discover1977/Wi-Fi-WEB-radio/Photo/20170609_091035.jpg

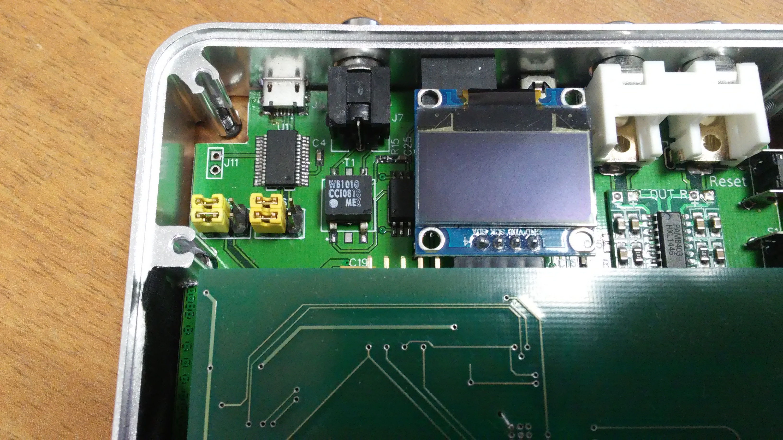
Photo/20170609_091035.jpg
