discover1977/Wi-Fi-WEB-radio/Photo/IMG_8502.JPG

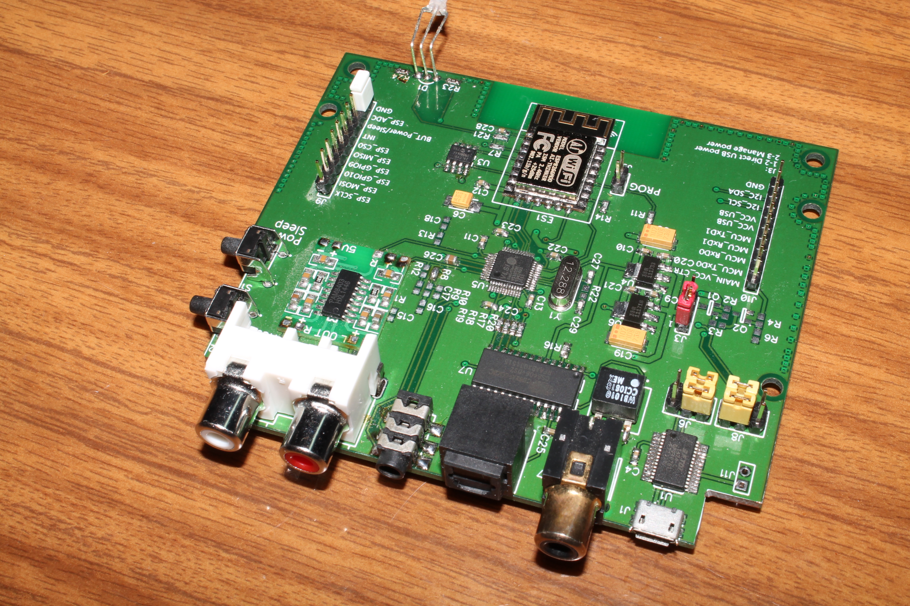
Photo/IMG_8502.JPG
