discover1977/Wi-Fi-WEB-radio/Photo/IMG_8504.JPG

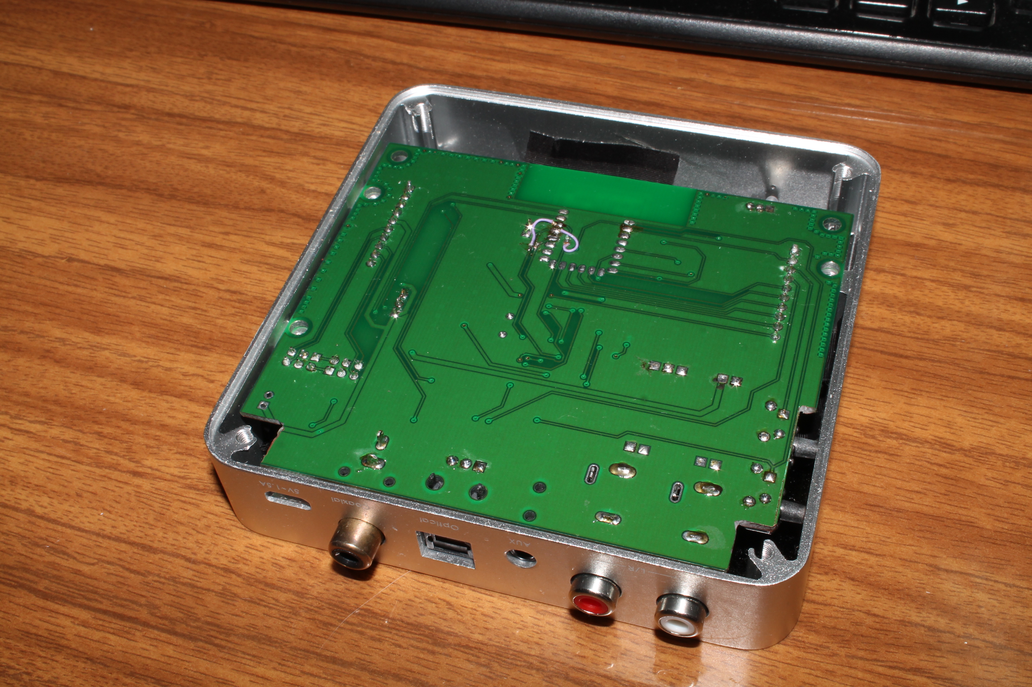
Photo/IMG_8504.JPG
