discover1977/Wi-Fi-WEB-radio/Photo/IMG_8505.JPG

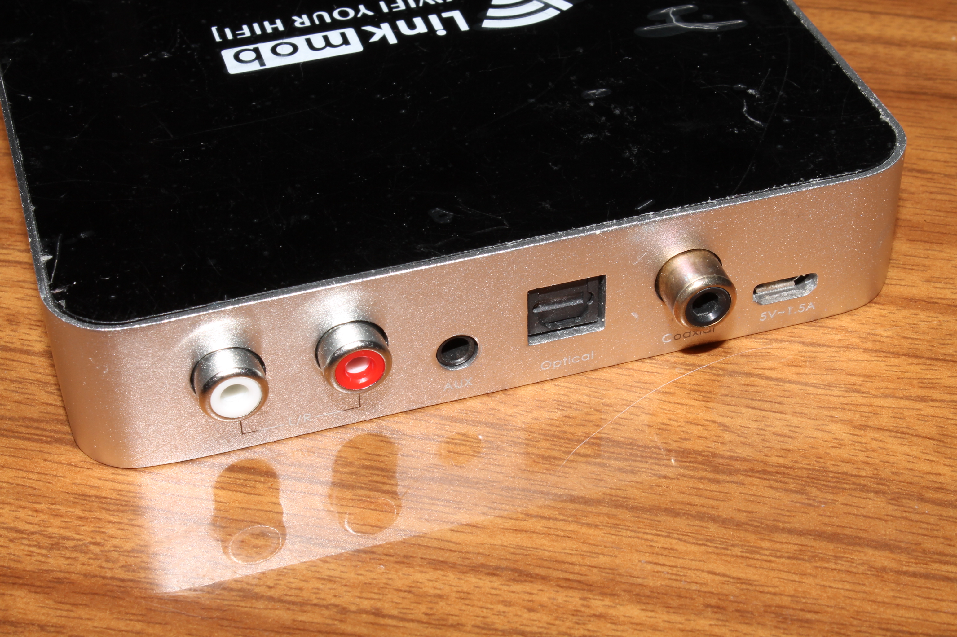
Photo/IMG_8505.JPG
