discover1977/Wi-Fi-WEB-radio/Photo/IMG_8543.JPG

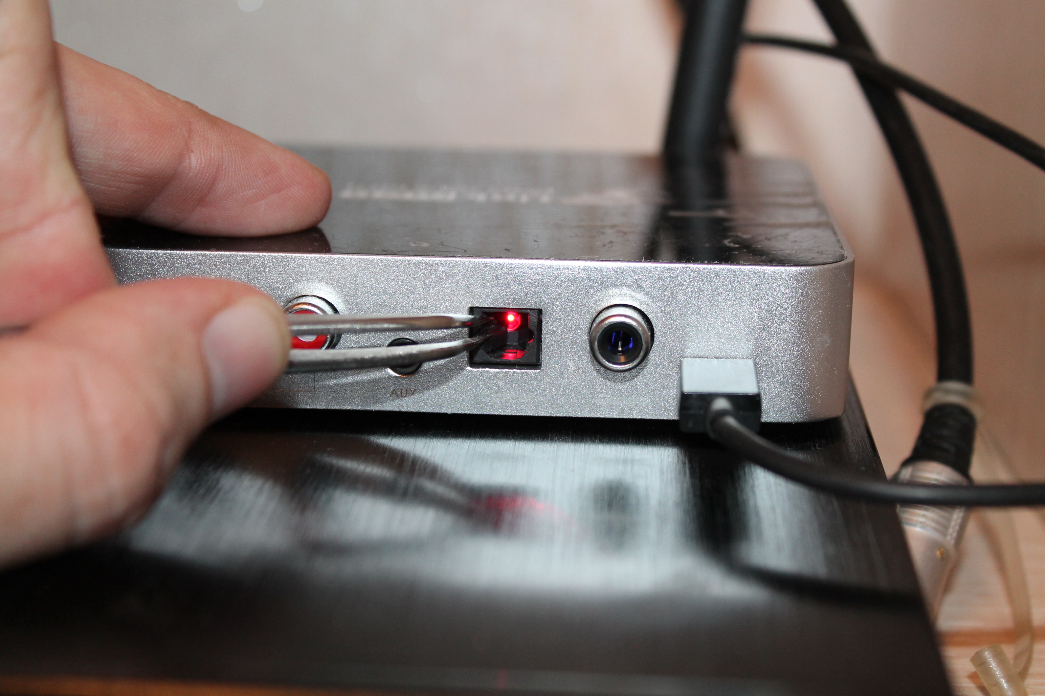
Photo/IMG_8543.JPG
