discover1977/Wi-Fi-WEB-radio/Photo/IMG_8549.JPG

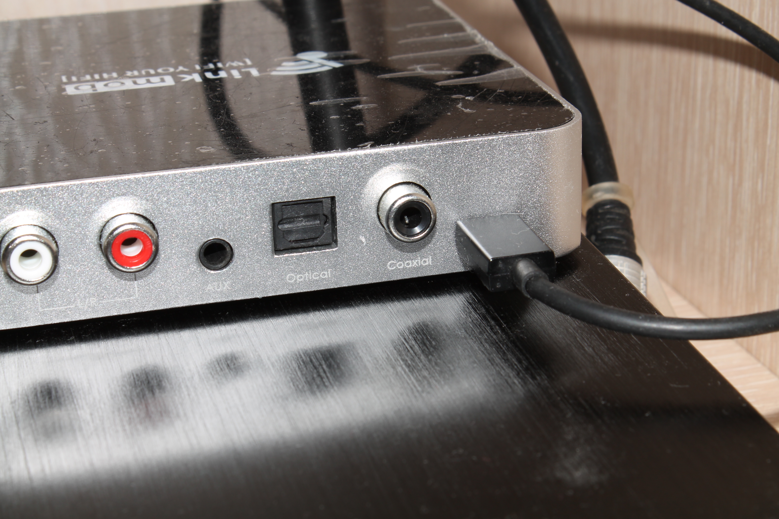
Photo/IMG_8549.JPG
