discover1977/Wi-Fi-WEB-radio/Photo/IMG_8566.JPG

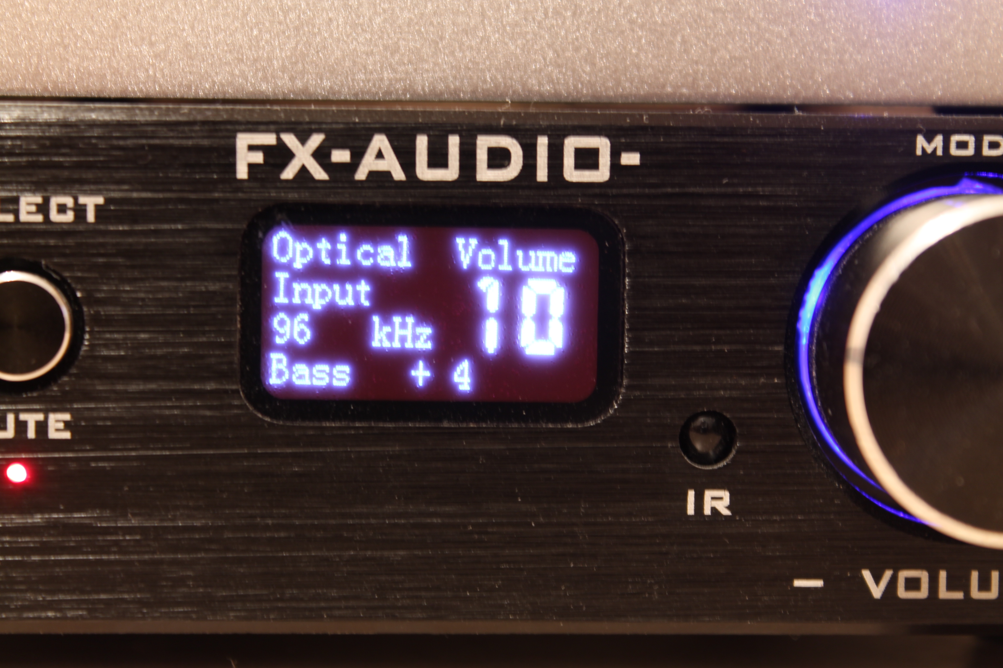
Photo/IMG_8566.JPG
