discover1977/Wi-Fi-WEB-radio/Photo/IMG_8903.JPG

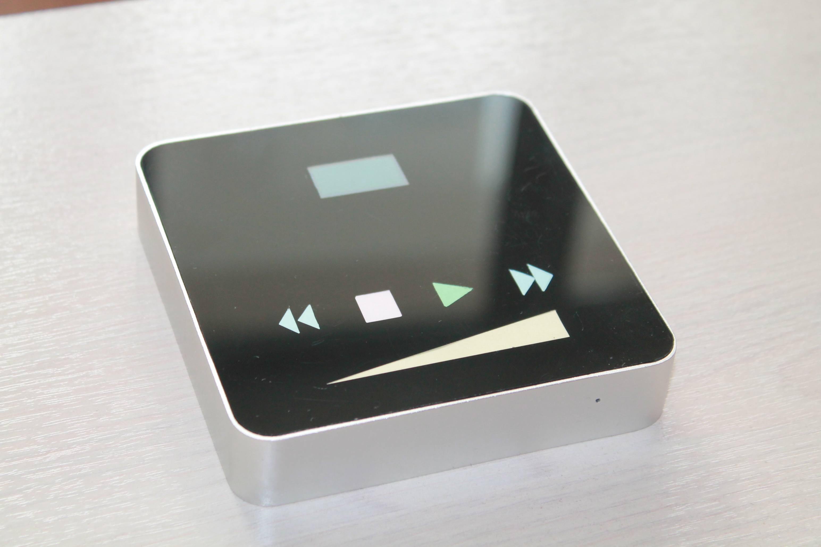
Photo/IMG_8903.JPG
