discover1977/Wi-Fi-WEB-radio/Photo/IMG_8904.JPG

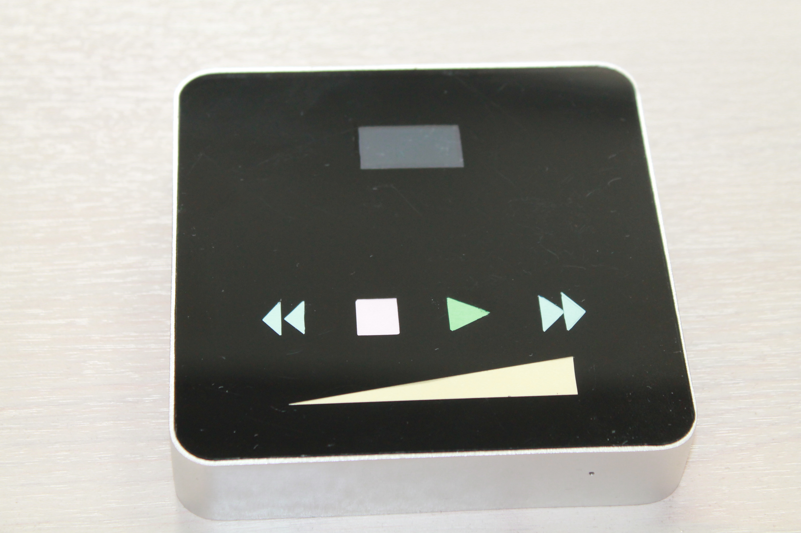
Photo/IMG_8904.JPG
