discover1977/Wi-Fi-WEB-radio/Photo/IMG_8905.JPG

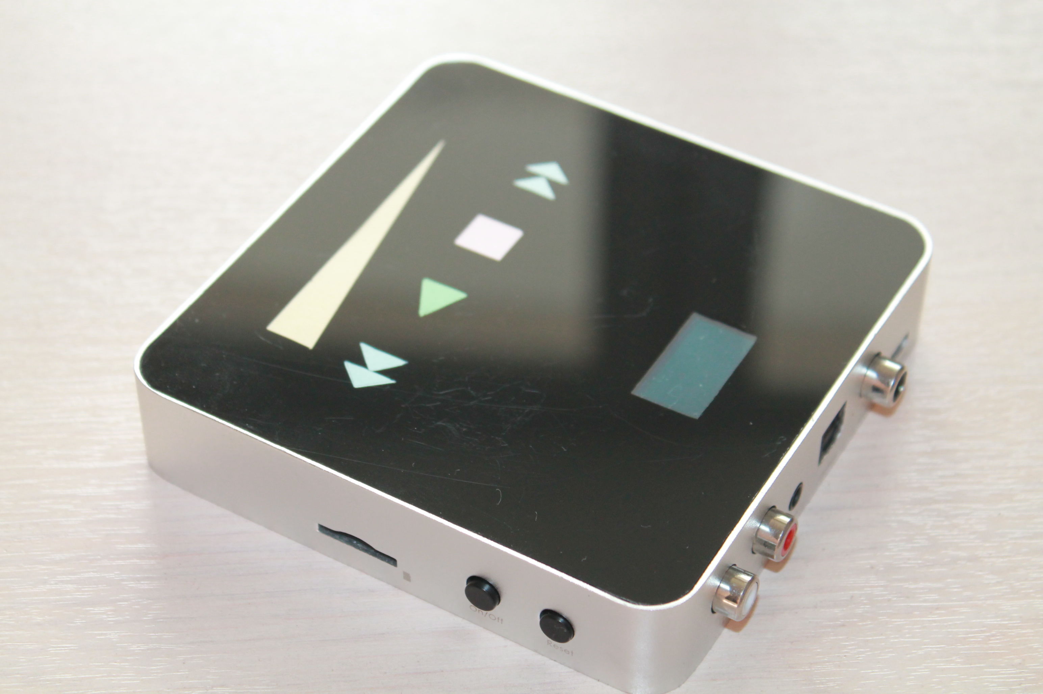
Photo/IMG_8905.JPG
