discover1977/Wi-Fi-WEB-radio/Photo/IMG_8907.JPG

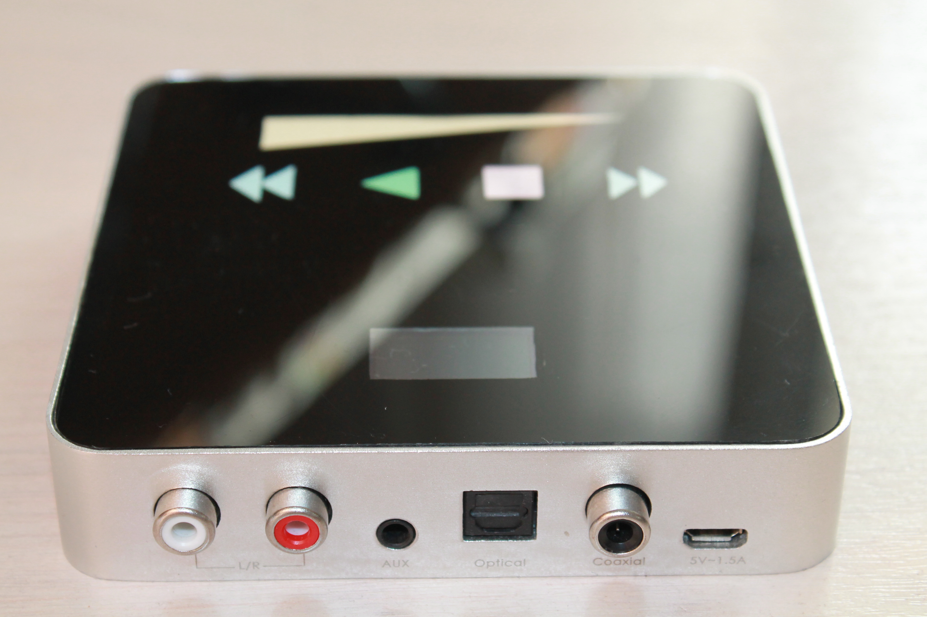
Photo/IMG_8907.JPG
