discover1977/Wi-Fi-WEB-radio/Control source/AVR_ touch_ control_OLED/TestMyBoard/src/TWI_driver.h

/*
 * TWI_driver.h
 *
 *  Created on: 30.05.2017
 *      Author: Gavrilov I.
 */

#ifndef TWI_DRIVER_H_
#define TWI_DRIVER_H_

#define HW

// Init Bus	
void TWI_Init();
// Start Transfer
void TWI_Start();
// Stop Transfer
void TWI_Stop();
// Write Transfer
unsigned int TWI_Write(unsigned int a);
// Read Transfer
unsigned int TWI_Read(unsigned int ack);

// Read Byte
unsigned int TWI_ReadByte(unsigned int nAddress, unsigned int nRegister);
// Write Byte
void TWI_WriteByte(unsigned int nAddress, unsigned int nRegister, unsigned int nValue);

#endif
