discover1977/Wi-Fi-WEB-radio/Control source/AVR_ touch_ control_OLED/TestMyBoard/touch.c

/* This source file is part of the ATMEL QTouch Library 5.0.8*/

/*****************************************************************************
 *
 * \file
 *
 * \brief  This file contains the Mega QTouch library initialization,
 * sensor configuration and measurement routines.
 *
 *
 * - Userguide:          QTouch Library Peripheral Touch Controller User Guide.
 * - Support email:      www.atmel.com/design-support/
 *
 *
 * Copyright (c) 2013-2015 Atmel Corporation. All rights reserved.
 *
 * \asf_license_start
 *
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
 * 3. The name of Atmel may not be used to endorse or promote products derived
 *    from this software without specific prior written permission.
 *
 * 4. This software may only be redistributed and used in connection with an
 *    Atmel microcontroller product.
 *
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
 * \asf_license_stop
 *
 ******************************************************************************/

/*----------------------------------------------------------------------------
 *                               include files
 *
 *
 *----------------------------------------------------------------------------*/

/**
 * Includes for Touch Library.
 */

#include "touch_api_ptc.h"
#include "touch.h"
#include "QDebug_mega.h"

/*----------------------------------------------------------------------------
 *                           manifest constants
 *
 *
 *----------------------------------------------------------------------------*/
#define   DEF_SELFCAP_CAL_SEQ1_COUNT                  8
#define   DEF_SELFCAP_CAL_SEQ2_COUNT                  4
#define DEF_SELFCAP_CC_CAL_CLK_PRESCALE_PER_NODE PRSC_DIV_SEL_1,PRSC_DIV_SEL_1,PRSC_DIV_SEL_1,PRSC_DIV_SEL_1,PRSC_DIV_SEL_1,PRSC_DIV_SEL_1,PRSC_DIV_SEL_1
#define DEF_SELFCAP_CC_CAL_SENSE_RESISTOR_PER_NODE RSEL_VAL_0,RSEL_VAL_0,RSEL_VAL_0,RSEL_VAL_0,RSEL_VAL_0,RSEL_VAL_0,RSEL_VAL_0
#define   DEF_SELFCAP_QUICK_REBURST_ENABLE            1u

/*----------------------------------------------------------------------------
 *                                   macros
 *
 *
 *----------------------------------------------------------------------------*/
#define  touch_std_err_handle() do{\
								  } while(1);
/*----------------------------------------------------------------------------
 *                           type definitions
 *
 *
 *----------------------------------------------------------------------------*/

/*----------------------------------------------------------------------------
 *                           Structure Declarations
 *
 *
 *----------------------------------------------------------------------------*/

/*----------------------------------------------------------------------------
 *                               global variables
 *
 *
 *----------------------------------------------------------------------------*/
/* ! QTouch Library Timing info. */
touch_time_t touch_time;

/* ! QTouch Library acquisition status */
touch_acq_status_t  touch_acq_status;

/**
 * Mutual Cap sensors measured data pointer.
 * Note: This pointer is initialized by the QTouch library once the
 * touch_mutlcap_sensors_init API is called. */
touch_measure_data_t *p_mutlcap_measure_data = NULL;

/**
 * Self Cap sensors measured data pointer.
 * Note: This pointer is initialized by the QTouch library once the
 * touch_selfcap_sensors_init API is called. */
touch_measure_data_t *p_selfcap_measure_data = NULL;


/*----------------------------------------------------------------------------
 *                               static variables
 *
 *
 *----------------------------------------------------------------------------*/

/**
 * Self Cap Data block provided as input to Touch library.
 */
static uint8_t selfcap_data_blk[PRIV_SELFCAP_DATA_BLK_SIZE];

/**
 * self Cap Sensor Pins Info.
 */

uint32_t selfcap_y_nodes[DEF_SELFCAP_NUM_CHANNELS] = {DEF_SELFCAP_LINES};

filter_level_t selfcap_filter_level_per_node[DEF_SELFCAP_NUM_CHANNELS] = {DEF_SELFCAP_FILTER_LEVEL_PER_NODE};

auto_os_t selfcap_auto_os_per_node[DEF_SELFCAP_NUM_CHANNELS]= {DEF_SELFCAP_AUTO_OS_PER_NODE};

gain_t selfcap_gain_per_node[DEF_SELFCAP_NUM_CHANNELS] = {DEF_SELFCAP_GAIN_PER_NODE};

rsel_val_t selfcap_resistor_per_node[DEF_SELFCAP_NUM_CHANNELS] = {DEF_SELFCAP_SENSE_RESISTOR_PER_NODE};

prsc_div_sel_t selfcap_prsc_per_node[DEF_SELFCAP_NUM_CHANNELS] = {DEF_SELFCAP_CLK_PRESCALE_PER_NODE};

prsc_div_sel_t selfcap_boot_prsc_per_node[DEF_SELFCAP_NUM_CHANNELS] =  {DEF_SELFCAP_CC_CAL_CLK_PRESCALE_PER_NODE};

rsel_val_t selfcap_boot_resistor_per_node[DEF_SELFCAP_NUM_CHANNELS] =  {DEF_SELFCAP_CC_CAL_SENSE_RESISTOR_PER_NODE};

freq_hop_sel_t selfcap_freq_hops[3u] = {DEF_SELFCAP_HOP_FREQS};

/**
 * self Cap Configuration structure provided as input to Touch Library.
 *
 * Note: Use the touch.h configuration header file to fill in
 * the elements of this structure.  DO NOT modify any of the input values
 * directly in this structure.
 */
static touch_selfcap_config_t selfcap_config =
{
    DEF_SELFCAP_NUM_CHANNELS,       /* Self Cap number of channels. */
    DEF_SELFCAP_NUM_SENSORS,        /* Self Cap number of sensors. */
    DEF_SELFCAP_NUM_ROTORS_SLIDERS, /* Self Cap number of rotors and
	                                 * sliders. */

    /* Self Cap GLOBAL SENSOR CONFIGURATION INFO. */
    {
        DEF_SELFCAP_DI,         /* uint8_t  di; Sensor detect
		                         * integration (DI) limit. */

        /* Interchanging Negative and Positive Drift rate, since Signal
         * increases on Touch. */
        DEF_SELFCAP_ATCH_DRIFT_RATE, /* uint8_t  neg_drift_rate; Sensor
		                              * negative drift rate. */
        DEF_SELFCAP_TCH_DRIFT_RATE, /* uint8_t  pos_drift_rate; Sensor
		                             * positive drift rate. */
        DEF_SELFCAP_MAX_ON_DURATION, /* uint8_t  max_on_duration; Sensor
		                              * maximum on duration. */
        DEF_SELFCAP_DRIFT_HOLD_TIME, /* uint8_t  drift_hold_time; Sensor
		                              * drift hold time. */
        DEF_SELFCAP_ATCH_RECAL_DELAY,   /* uint8_t  pos_recal_delay;
		                                 * Sensor positive recalibration
		                                 * delay. */
        DEF_SELFCAP_CAL_SEQ1_COUNT,
        DEF_SELFCAP_CAL_SEQ2_COUNT,
        DEF_SELFCAP_ATCH_RECAL_THRESHOLD, /* recal_threshold_t
		                                   * recal_threshold; Sensor
		                                   * recalibration threshold. */
        DEF_SELFCAP_TOUCH_POSTPROCESS_MODE,
        DEF_SELFCAP_AUTO_OS_SIGNAL_STABILITY_LIMIT,
        DEF_SELFCAP_FREQ_AUTO_TUNE_SIGNAL_STABILITY_LIMIT,
        DEF_SELFCAP_FREQ_AUTO_TUNE_IN_CNT,
        DEF_SELFCAP_NOISE_MEAS_SIGNAL_STABILITY_LIMIT, /* signal
		                                                *stability */
        DEF_SELFCAP_NOISE_LIMIT,
        DEF_SELFCAP_LOCKOUT_SEL,
        DEF_SELFCAP_LOCKOUT_CNTDOWN,
        DEF_SELF_CAP_CSD_VALUE,
    },
    {
        selfcap_gain_per_node,      /* Self Cap channel gain setting. */
        DEF_SELFCAP_FREQ_MODE,      /* Self Cap noise counter measure
		                             * enable/disable. */
        selfcap_prsc_per_node,
        selfcap_resistor_per_node,
        selfcap_boot_prsc_per_node,
        selfcap_boot_resistor_per_node,
        selfcap_freq_hops,
        selfcap_filter_level_per_node,   /* Self Cap filter level setting. */
        selfcap_auto_os_per_node,        /* Self Cap auto oversamples
		                             *setting. */
    },
    selfcap_data_blk,                   /* Self Cap data block index. */
    PRIV_SELFCAP_DATA_BLK_SIZE,         /* Self Cap data block size. */
    selfcap_y_nodes,                    /* Self Cap channel nodes. */
    DEF_SELFCAP_QUICK_REBURST_ENABLE,
    DEF_SELFCAP_FILTER_CALLBACK,         /* Self Cap filter callback
	                                      * function
	                                      * pointer. */
    DEF_SELFCAP_FREQ_AUTO_TUNE_ENABLE,
    DEF_SELFCAP_NOISE_MEAS_ENABLE,
    DEF_SELFCAP_NOISE_MEAS_BUFFER_CNT,
    DEF_SELFCAP_MOIS_TOLERANCE_ENABLE,
    DEF_SELFCAP_NUM_MOIS_GROUPS,
    DEF_SELFCAP_MOIS_QUICK_REBURST_ENABLE,
    DEF_SELFCAP_PTC_GPIO_STATE,
    .tlib_feature_list ={
        .lk_chk = DEF_LOCKOUT_FUNC,
        .auto_os_init = DEF_AUTO_OS_FUNC,//auto_os_resolve,
        .auto_tune_init = DEF_SELF_AUTO_TUNE_FUNC,// self_auto_tuning
        .enable_aks = DEF_AKS_FUNC, /*AKS grouping function */
    }
};

/**
 * Touch Library input configuration structure.
 */
touch_config_t touch_config =
{
    NULL,

    &selfcap_config,	/* Pointer to self Cap configuration structure. */

    TCH_MODE_ISR,    /* Touch Mode */
};

/*----------------------------------------------------------------------------
 *                               prototypes
 *
 *
 *----------------------------------------------------------------------------*/

/*! \brief configure keys, rotors and sliders.
 */
touch_ret_t touch_sensors_config(void);

/*! \brief touch application error handler.
 */
void touch_app_err_handler(touch_app_err_t touch_app_err_val, touch_ret_t touch_lib_err_val);

/*! \brief self Cap measure complete callback function example prototype.
 */
void touch_selfcap_measure_complete_callback( void );
/*----------------------------------------------------------------------------
 *  Functions defines
 *
 *
 *----------------------------------------------------------------------------*/
/*! \brief Error handler to trap the touch error
 *
 * \param touch_app_err_t   Error code indicates error source
 * \param touch_lib_err_val  Error code indicating the error type for error source
 * \return void
 */
void  __attribute__((optimize("O0"))) touch_app_err_handler(touch_app_err_t touch_app_err_val, touch_ret_t touch_lib_err_val)
{
	if(DEF_TOUCH_APP_ERR_HANDLER)
	
	{
    switch(touch_app_err_val)
    {
    case TOUCH_INIT_CONFIG_ERR:
        /*Probable reason: the touch_xxxxcap_sensors_init is fed with an
         incompatible / incomplete parameter*/
        touch_std_err_handle();
        break;
    case TOUCH_SENSOR_CONFIG_ERR:
        /*Probable reason: touch_xxxxcap_sensor_config is fed with an incompatible
         parameter / Library state is not INIT*/
        touch_std_err_handle();
        break;
    case TOUCH_INIT_CALIB_ERR:
        /*Probable reason: the touch_xxxxcap_sensors_calibrate is fed with an
        invalid parameter / the LIB state is NONE/BUSY */
        touch_std_err_handle();
        break;
    case TOUCH_MEASURE_INCOMPLETE:
        /* Reaching this point can be due to - The touch_measure api has error
        due to a invalid input param / it was on an invalid Touch Library state*/
        touch_std_err_handle();
        break;
    case TOUCH_MEASURE_CC_CAL_FAILED:
        /*Probable reason: Hardware calibration error, check the hardware,
          and ensure it is proper, if the error persists check the user manual
          for sensor design guidelines*/
        touch_std_err_handle();
        break;
    default:
        touch_std_err_handle();
        break;
    }
	}
}

/*! \brief Example application entry function.
 */
touch_ret_t touch_sensors_init(void)
{

    touch_ret_t touch_ret = TOUCH_SUCCESS;

    touch_time.measurement_period_ms = DEF_TOUCH_MEASUREMENT_PERIOD_MS;

    /* Initialize touch library for self Cap operation. */
    touch_ret = touch_selfcap_sensors_init(&touch_config);
    if (touch_ret != TOUCH_SUCCESS)
    {
        touch_app_err_handler(TOUCH_INIT_CONFIG_ERR, touch_ret);
    }

#if DEF_TOUCH_QDEBUG_ENABLE == 1
    QDebug_Init();
#endif


    /* configure the touch library sensors. */
    touch_ret = touch_sensors_config();
    if (touch_ret != TOUCH_SUCCESS)
    {
        touch_app_err_handler(TOUCH_SENSOR_CONFIG_ERR, touch_ret);
    }

    /* Auto Tuning setting for calibration.
     *
     * AUTO_TUNE_PRSC: When Auto tuning of pre-scaler is selected
     * the PTC uses the user defined internal series resistor setting
     * (DEF_SELFCAP_SENSE_RESISTOR) and the pre-scaler is adjusted
     * to slow down the PTC operation to ensure full charge transfer.
     *
     * AUTO_TUNE_RSEL: When Auto tuning of the series resistor is
     * selected the PTC runs at user defined pre-scaler setting speed
     * (DEF_SELFCAP_CLK_PRESCALE) and the internal series resistor is
     * tuned automatically to the optimum value to allow for full
     * charge transfer.
     *
     * AUTO_TUNE_NONE: When manual tuning option is selected
     *(AUTO_TUNE_NONE),
     * the user defined values of PTC pre-scaler and series resistor is used
     * for PTC operation as given in DEF_SELFCAP_CLK_PRESCALE and
     * DEF_SELFCAP_SENSE_RESISTOR
     *
     */
    touch_ret = touch_selfcap_sensors_calibrate(DEF_SELF_AUTO_TUNE_VALUE);
    if (touch_ret != TOUCH_SUCCESS)
    {
        touch_app_err_handler(TOUCH_INIT_CALIB_ERR, touch_ret);
    }

    return (touch_ret);
}

/*! \brief Example touch measure function for selfcap
 * \param void
 *
 * \retval TOUCH_SUCCESS   measurement is initiated.
 * \retval TOUCH_ACQ_INCOMPLETE  PTC is busy.
 */
touch_ret_t touch_sensors_measure(void)
{
    touch_ret_t touch_ret = TOUCH_SUCCESS;
    uint8_t touch_process_ongoing ;
    if (!(p_selfcap_measure_data->acq_status & TOUCH_CC_CALIB_ERROR) || (!DEF_TOUCH_APP_ERR_HANDLER))
    {
        touch_process_ongoing = touch_ptc_process();

        if ((touch_time.time_to_measure_touch == 1u) && (touch_process_ongoing == 0u))
        {
            /* Start a touch sensors measurement process. */

            touch_ret = touch_selfcap_sensors_measure(
                            touch_time.current_time_ms,
                            NORMAL_ACQ_MODE,
                            touch_selfcap_measure_complete_callback);

            if ((touch_ret != TOUCH_ACQ_INCOMPLETE) &&
                    (touch_ret == TOUCH_SUCCESS))
            {
                touch_time.time_to_measure_touch = 0u;
            }/*if*/
            else if ((touch_ret != TOUCH_SUCCESS) &&
                     (touch_ret != TOUCH_ACQ_INCOMPLETE))
            {
                /* Reaching this point can be due to -
                 *     1. The api has retured an error due to a invalid
                 * input parameter.
                 *     2. The api has been called during a invalid Touch
                 * Library state. */
                touch_app_err_handler(TOUCH_MEASURE_INCOMPLETE, touch_ret);
            }/*else*/
        }/*if*/
    }/*if*/

    else
    {
        /**
         * Hardware calibration error, check the hardware,
         * and ensure it is proper, if the error persists
         * check the user manual for design guidelines
         */

        /**
         * To find which sensor failed in the calibration, check
         * p_xxxxcap_measure_data->p_sensors[<sensor>].state == SENSOR_CALIBRATION_ERROR
         */

        touch_app_err_handler(TOUCH_MEASURE_CC_CAL_FAILED, touch_ret);
    }/*else*/
    return (touch_ret);
}

/*! \brief Example configuration for touch keys, rotors and sliders.
 *
 * \retval TOUCH_SUCCESS   Configuration setting successful.
 * \retval TOUCH_INVALID_xx   Invalid input configuration setting.
 */
touch_ret_t touch_sensors_config(void)
{
    touch_ret_t touch_ret = TOUCH_SUCCESS;
    sensor_id_t sensor_id;

    	touch_ret = touch_selfcap_sensor_config(SENSOR_TYPE_KEY, CHANNEL_0,CHANNEL_0, NO_AKS_GROUP, 10u, HYST_25,RES_8_BIT, &sensor_id);
	if (touch_ret != TOUCH_SUCCESS)
	{
		 touch_app_err_handler(TOUCH_SENSOR_CONFIG_ERR, touch_ret); 
	}


	touch_ret = touch_selfcap_sensor_config(SENSOR_TYPE_KEY, CHANNEL_1,CHANNEL_1, NO_AKS_GROUP, 10u, HYST_25,RES_8_BIT, &sensor_id);
	if (touch_ret != TOUCH_SUCCESS)
	{
		 touch_app_err_handler(TOUCH_SENSOR_CONFIG_ERR, touch_ret); 
	}


	touch_ret = touch_selfcap_sensor_config(SENSOR_TYPE_KEY, CHANNEL_2,CHANNEL_2, NO_AKS_GROUP, 10u, HYST_25,RES_8_BIT, &sensor_id);
	if (touch_ret != TOUCH_SUCCESS)
	{
		 touch_app_err_handler(TOUCH_SENSOR_CONFIG_ERR, touch_ret); 
	}


	touch_ret = touch_selfcap_sensor_config(SENSOR_TYPE_KEY, CHANNEL_3,CHANNEL_3, NO_AKS_GROUP, 10u, HYST_25,RES_8_BIT, &sensor_id);
	if (touch_ret != TOUCH_SUCCESS)
	{
		 touch_app_err_handler(TOUCH_SENSOR_CONFIG_ERR, touch_ret); 
	}


	touch_ret = touch_selfcap_sensor_config(SENSOR_TYPE_SLIDER, CHANNEL_4,CHANNEL_6, NO_AKS_GROUP, 10u, HYST_25,RES_8_BIT, &sensor_id);
	if (touch_ret != TOUCH_SUCCESS)
	{
		 touch_app_err_handler(TOUCH_SENSOR_CONFIG_ERR, touch_ret); 
	}






    return (touch_ret);
}

/*! \brief self Cap measure complete callback function.
 *
 * This function is called by the library when the touch measurement
 * process for self Cap sensors is completed.
 *
 * \param p_measure_data   Base address of touch_measure_data_t instance.
 * \note A touch_selfcap_measure_complete_callback() call signifies that fresh
 * values of touch status, rotor/slider position, measured signals,
 * references and Sensor data is available.
 * The self Cap measured data can be accessed using the p_measure_data
 * pointer.
 */
void touch_selfcap_measure_complete_callback( void )
{
	if ((p_selfcap_measure_data->acq_status & TOUCH_BURST_AGAIN) == 0u)
    {
#if DEF_TOUCH_QDEBUG_ENABLE == 1

    /* Send out the Touch debug information data each time when Touch
     *   measurement process is completed .
     *   The Touch Signal and Touch Delta values are always sent.
     *   Touch Status change, Rotor-Slider Position change and Sensor
     * Reference
     *   values can be optionally sent using the masks below.
     */
    QDebug_SendData( TOUCH_CHANNEL_REF_CHANGE |
                     TOUCH_ROTOR_SLIDER_POS_CHANGE |
                     TOUCH_STATUS_CHANGE );

    QDebug_ProcessCommands();


#endif
        /* Set the self Cap measurement done flag. */
        p_selfcap_measure_data->measurement_done_touch = 1u;
		touch_acq_status = p_selfcap_measure_data->acq_status;
    }
}
