discover1977/Wi-Fi-WEB-radio/Control source/AVR_ touch_ control_OLED/TestMyBoard/TWI_SW_Master.c

/*
 * i2c-soft.c
 *
 *  Created on: 19.12.2009
 *      Author: Pavel V. Gololobov
 */
#include <avr/io.h>
#include "TWI_SW_Master.h"

//------------------------------------------------------------------
// I2C Speed Down
//------------------------------------------------------------------
#define I2CWAIT TWI_SW_Wait(1);

//------------------------------------------------------------------
// I2C Delay
//------------------------------------------------------------------
void TWI_SW_Wait(unsigned int n)
{
	do
	{
		asm("nop");
		//asm("nop");
		//asm("nop");
		//asm("nop");
		//asm("nop");
	}
	while(--n);
}

//------------------------------------------------------------------
// I2C SDA SCL Control
//------------------------------------------------------------------
static void SetLowSDA()
{
	I2CDIR |= SDA;
	I2CWAIT
}
static void SetHighSDA()
{
	I2CDIR &= ~SDA;
	I2CWAIT
}

static void SetLowSCL()
{
	I2COUT &= ~SCL;
	I2CWAIT
}
static void SetHighSCL()
{
	I2COUT |= SCL;
	I2CWAIT
}

//------------------------------------------------------------------
// I2C Initialize Bus
//------------------------------------------------------------------
void TWI_SW_Init()
{
	I2CSEL &= ~SDA;
	I2CSEL &= ~SCL;

	I2COUT &= ~SCL;
	I2COUT &= ~SDA;

	I2CDIR |= SCL;
	I2CDIR &= ~SDA;

	SetHighSCL();
	SetLowSDA();
	SetHighSDA();
}

//------------------------------------------------------------------
// I2C Start Data Transfer
//------------------------------------------------------------------
void TWI_SW_Start()
{
	SetHighSCL();
	SetHighSDA();

	SetHighSCL();
	SetLowSDA();

	SetLowSCL();
	SetHighSDA();
}

//------------------------------------------------------------------
// I2C Stop  Transfer
//------------------------------------------------------------------
void TWI_SW_Stop()
{
	SetLowSCL();
	SetLowSDA();

	SetHighSCL();
	SetLowSDA();

	SetHighSCL();
	SetHighSDA();
}

//------------------------------------------------------------------
// I2C Write  Transfer
//------------------------------------------------------------------
unsigned int TWI_SW_Write(unsigned int a)
{
	unsigned int i;
	unsigned int return_ack;

	for (i = 0; i < 8; i++)
    {
		SetLowSCL();
		if (a & 0x80)
			SetHighSDA();
		else
			SetLowSDA();

		SetHighSCL();
		a <<= 1;
	}
	SetLowSCL();

	/* ack Read */
	SetHighSDA();
	SetHighSCL();

	if (I2CIN & SDA)
		return_ack = NO_TWI_SW_ACK;
	else
		return_ack = OK_TWI_SW_ACK;
	
    SetLowSCL();

	return (return_ack);
}

//------------------------------------------------------------------
// I2C Read  Transfer
//------------------------------------------------------------------
unsigned int TWI_SW_Read(unsigned int ack)
{
	unsigned int i;
	unsigned int caracter = 0x00;

	SetLowSCL();
	SetHighSDA();

	for (i = 0; i < 8; i++)
    {
		caracter = caracter << 1;
		SetHighSCL();
		if (I2CIN & SDA)
			caracter = caracter  + 1;
        
		SetLowSCL();
	}

	if (ack)
    {
		SetLowSDA();
	}
	SetHighSCL();
	SetLowSCL();

	return (caracter);
}

//------------------------------------------------------------------
// I2C Read Byte
//------------------------------------------------------------------
unsigned int TWI_SW_ReadByte(unsigned int nAddress, unsigned int nRegister)
{
	TWI_SW_Start();
	TWI_SW_Write(nAddress);
	TWI_SW_Write(nRegister);
	TWI_SW_Start();
	TWI_SW_Write(nAddress | 0x01);
	uint8_t ret = TWI_SW_Read(0);
	TWI_SW_Stop();

	return ret;
}

//------------------------------------------------------------------
// I2C Write Byte
//------------------------------------------------------------------
void TWI_SW_WriteByte(unsigned int nAddress, unsigned int nRegister, unsigned int nValue)
{
	TWI_SW_Start();
	TWI_SW_Write(nAddress);
	TWI_SW_Write(nRegister);
	TWI_SW_Write(nValue);
	TWI_SW_Stop();
}
